hello3dprintingworld/helloprinter/Bed/Bed Corner Extruder x2.stl

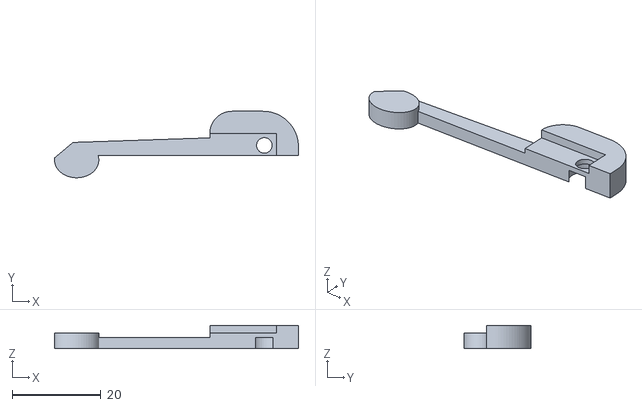
[picture p15: CAD file, 2015-12-08]
Bed/Bed Corner Extruder x2.stl
55.0 x 15.0 x 5.20
