hello3dprintingworld/helloprinter/Controllers/RAMPS 14/RAMPS FRONT.stl

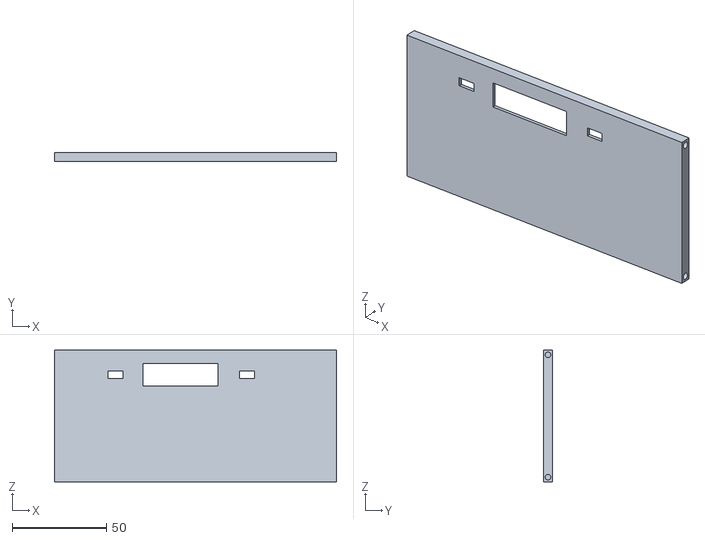
[picture p16: CAD file, 2014-11-10]
Controllers/RAMPS 14/RAMPS FRONT.stl
150.0 x 5.00 x 70.0
