hello3dprintingworld/helloprinter/Eixo X/5mm/x axis idler.stl

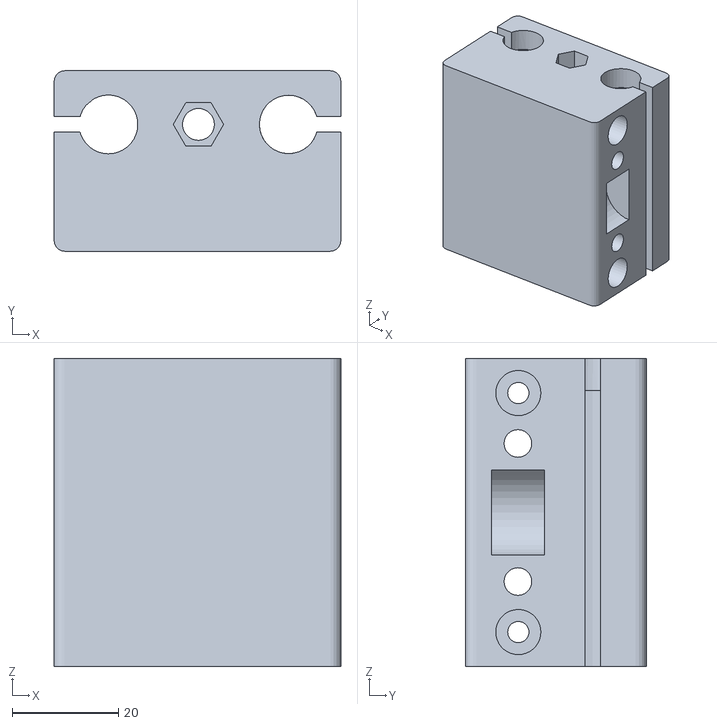
[picture p18: CAD file, 2015-12-08]
Eixo X/5mm/x axis idler.stl
54.0 x 34.0 x 58.0
