hello3dprintingworld/helloprinter/Eixo Z/Z motor x2.stl

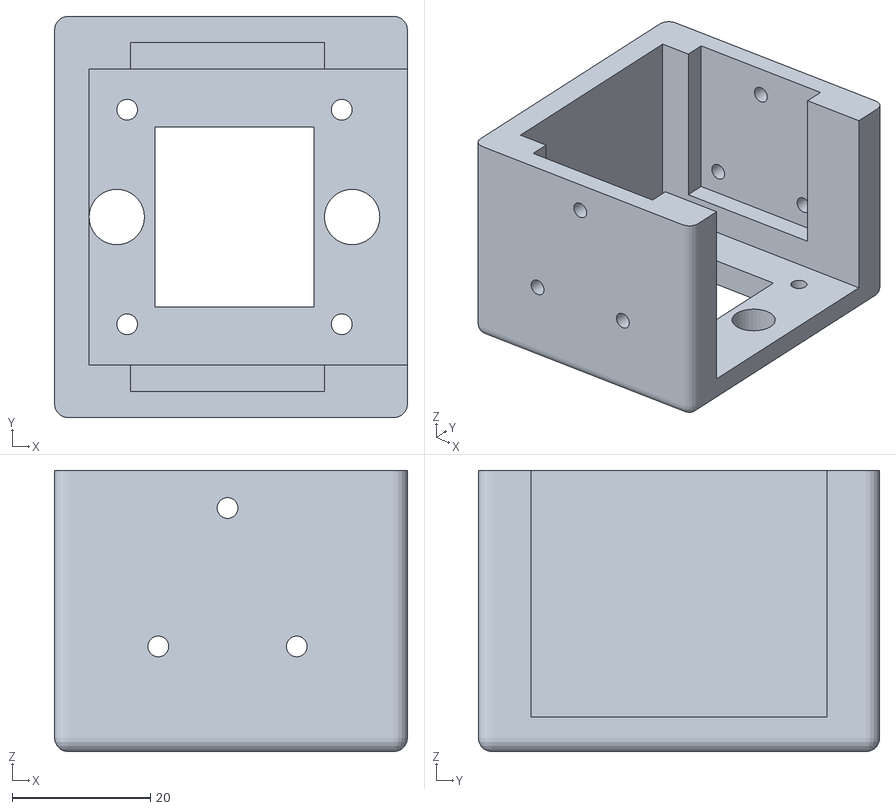
[picture p19: CAD file, 2015-12-08]
Eixo Z/Z motor x2.stl
51.0 x 58.0 x 40.6
