hello3dprintingworld/helloprinter/Endstops/endstop-holder-bottom x3.stl

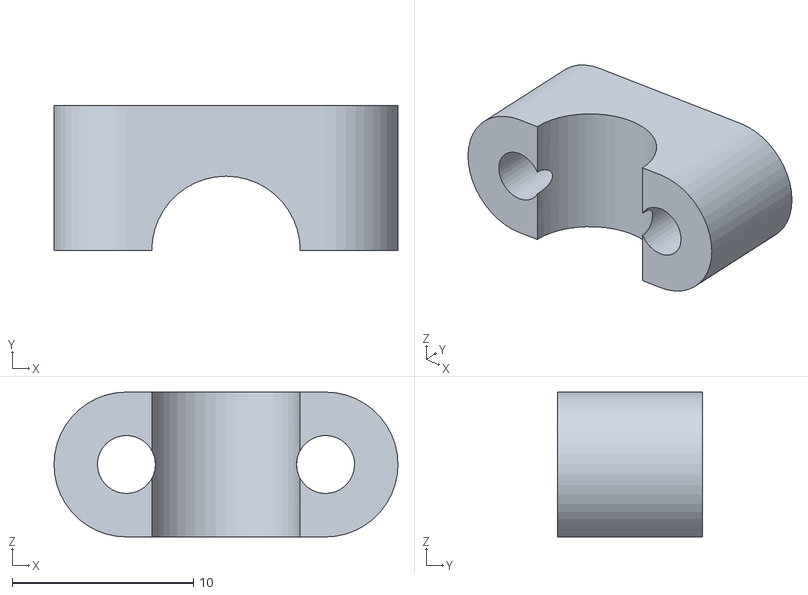
[picture p20: CAD file, 2015-12-08]
Endstops/endstop-holder-bottom x3.stl
19.0 x 8.00 x 8.00
