hello3dprintingworld/helloprinter/Extruder/Single Extruder for dual mirror parts/x belt.STL

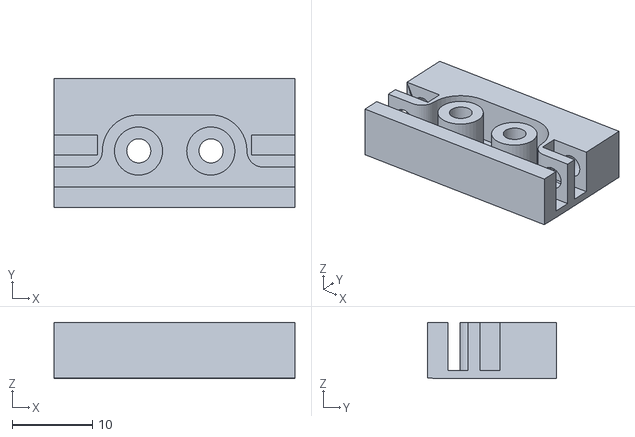
[picture p21: CAD file, 2015-12-08]
Extruder/Single Extruder for dual mirror parts/x belt.STL
30.0 x 16.0 x 7.00
