hello3dprintingworld/helloprinter/LCD/LCD Knob.stl

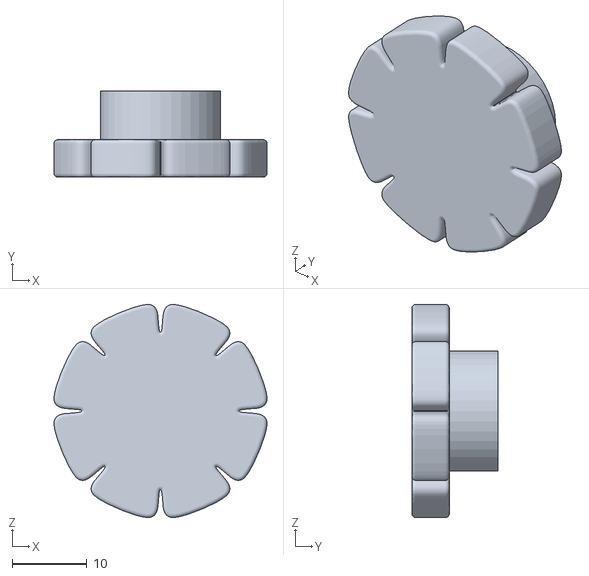
[picture p22: CAD file, 2014-11-10]
LCD/LCD Knob.stl
28.4 x 11.5 x 28.4
