hello3dprintingworld/helloprinter/Plug and switch/Plug and switch back x1.STL

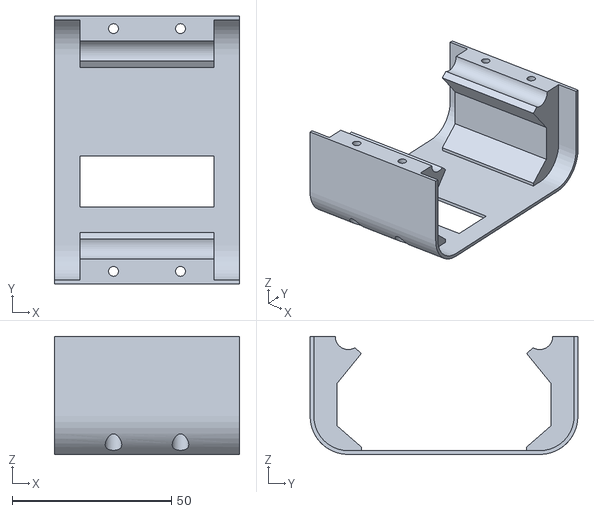
[picture p23: CAD file, 2015-12-08]
Plug and switch/Plug and switch back x1.STL
58.0 x 84.0 x 37.0
