hello3dprintingworld/helloprinter/Power Supply/PSU Cover x1.stl

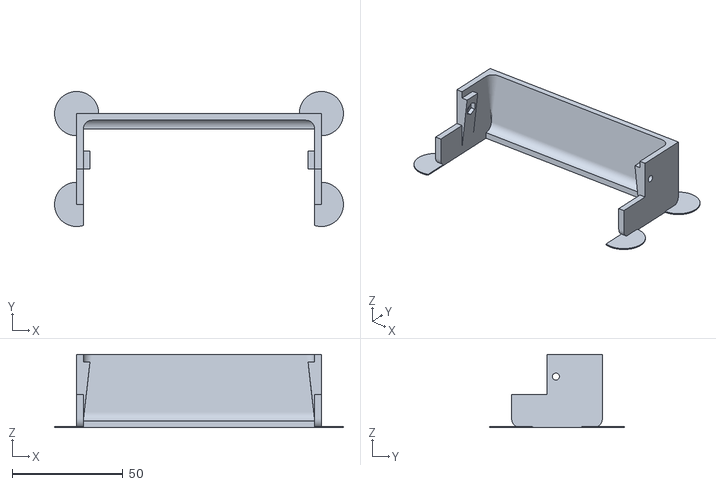
[picture p24: CAD file, 2015-12-08]
Power Supply/PSU Cover x1.stl
130.5 x 61.0 x 33.0
