hello3dprintingworld/helloprinter/Reinforcement XL/Part1.SLDPRT

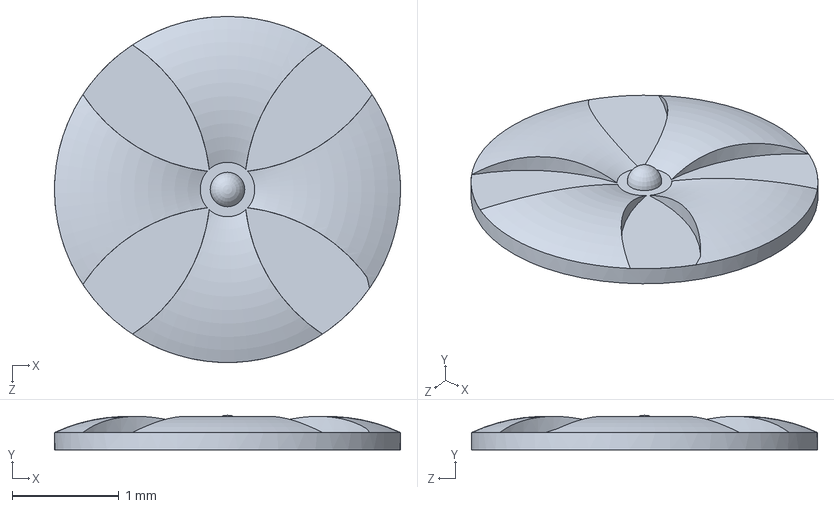
[picture p25: CAD file, 2015-12-08]
Reinforcement XL/Part1.SLDPRT
3.24 x 0.324 x 3.24 mm
