hello3dprintingworld/helloprinter/Spool Holder/Spool Holder.stl

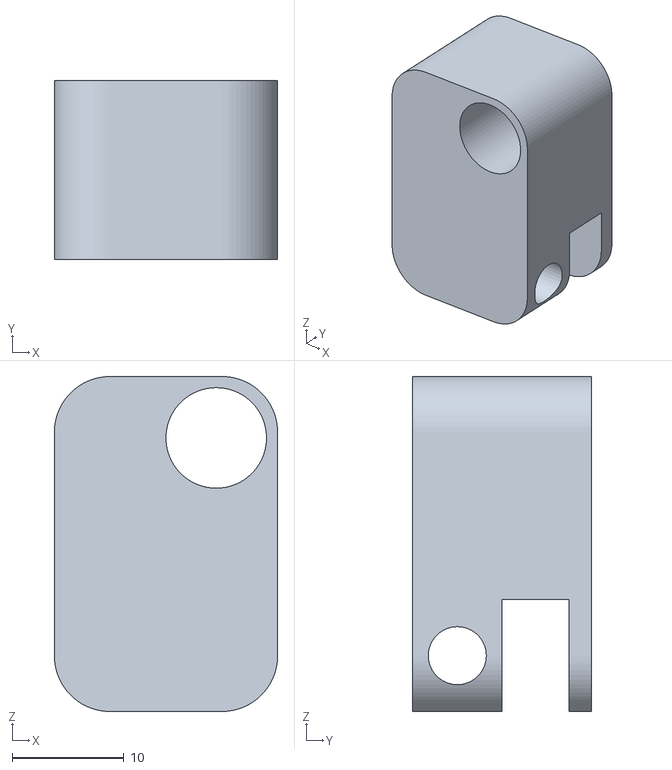
[picture p26: CAD file, 2015-12-08]
Spool Holder/Spool Holder.stl
20.0 x 16.0 x 30.0
