hello3dprintingworld/helloprinter/Bed/Bed corners normal x2.stl

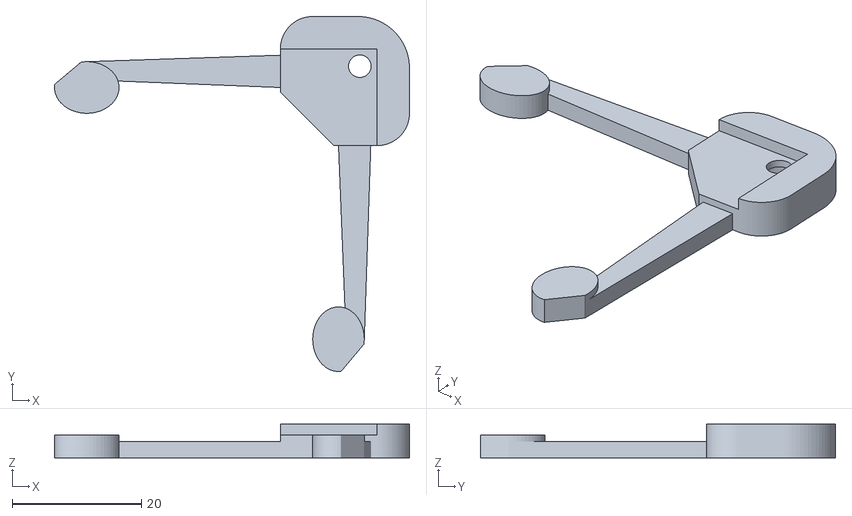
[picture p27: CAD file, 2015-12-08]
Bed/Bed corners normal x2.stl
55.0 x 55.0 x 5.20
