hello3dprintingworld/helloprinter/Controllers/RAMPS 14/RAMPS BOTTOM 1X.stl

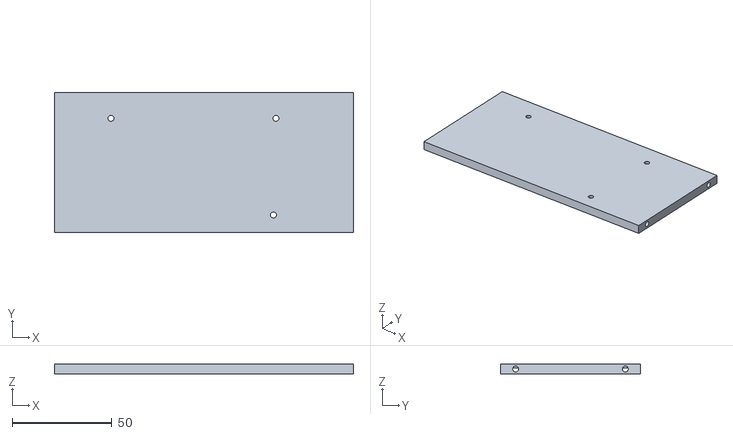
[picture p28: CAD file, 2014-11-10]
Controllers/RAMPS 14/RAMPS BOTTOM 1X.stl
150.0 x 70.0 x 5.00
