hello3dprintingworld/helloprinter/Controllers/RUMBA/LCD back.stl

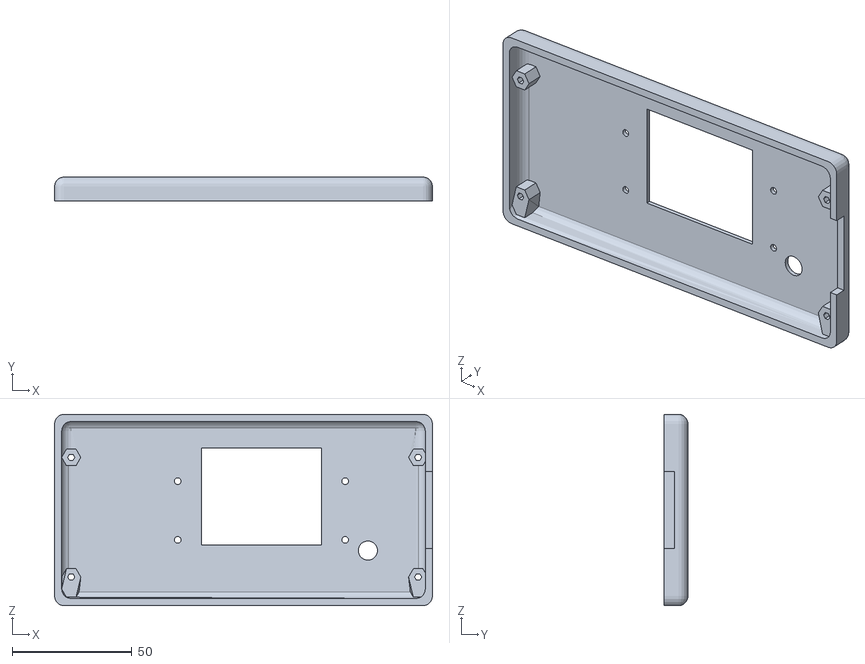
[picture p29: CAD file, 2015-12-08]
Controllers/RUMBA/LCD back.stl
158.0 x 10.1 x 80.0
