hello3dprintingworld/helloprinter/Eixo X/5mm/x axis idler tensioner.stl

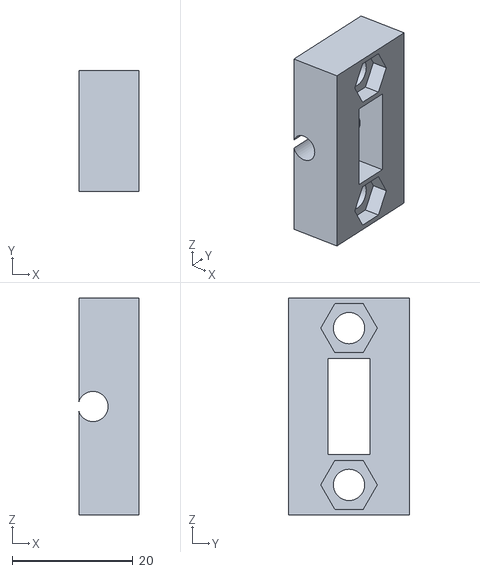
[picture p30: CAD file, 2015-12-08]
Eixo X/5mm/x axis idler tensioner.stl
10.0 x 20.0 x 36.0
