hello3dprintingworld/helloprinter/Eixo Y/Y Motor.stl

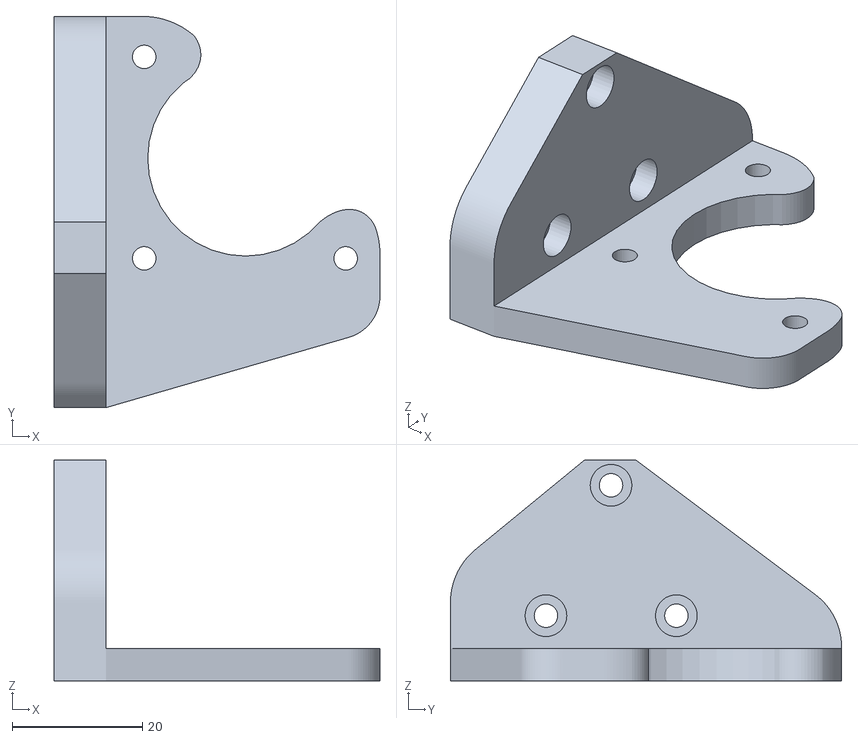
[picture p31: CAD file, 2014-07-07]
Eixo Y/Y Motor.stl
50.0 x 60.0 x 33.9
