hello3dprintingworld/helloprinter/Endstops/endstop-holder-top x3.stl

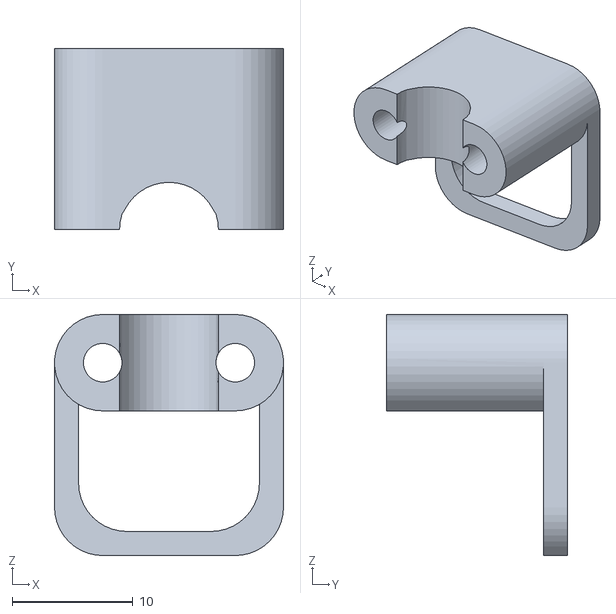
[picture p32: CAD file, 2015-12-08]
Endstops/endstop-holder-top x3.stl
19.0 x 15.0 x 20.0
