hello3dprintingworld/helloprinter/Extruder/Single Extruder for dual mirror parts/fan.STL

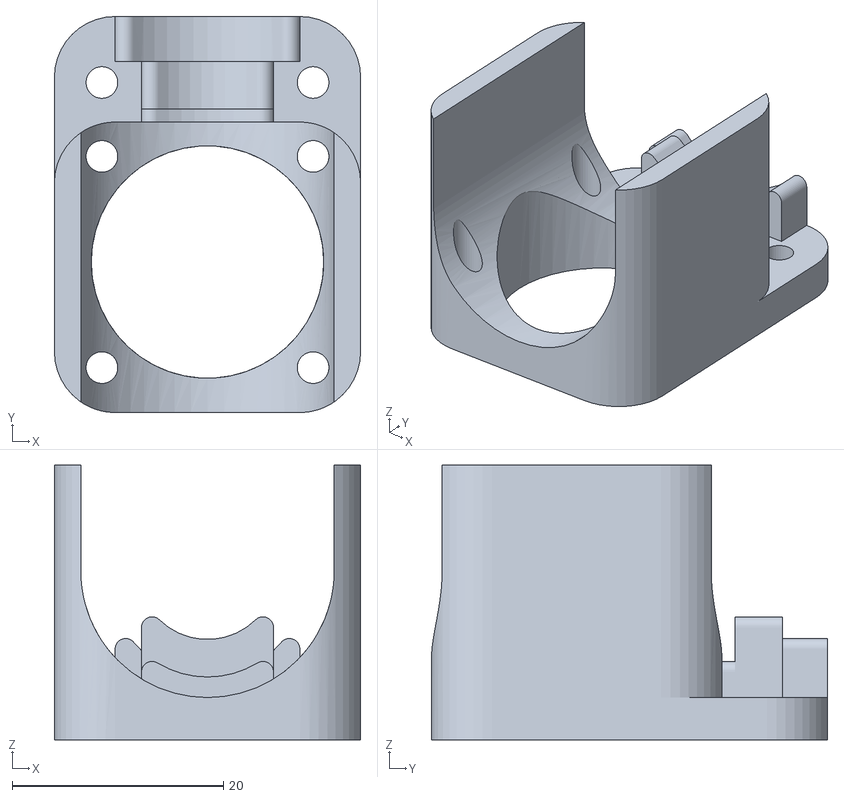
[picture p33: CAD file, 2015-12-08]
Extruder/Single Extruder for dual mirror parts/fan.STL
29.0 x 37.5 x 26.0
