hello3dprintingworld/helloprinter/Power Supply/Cable Guide BED.stl

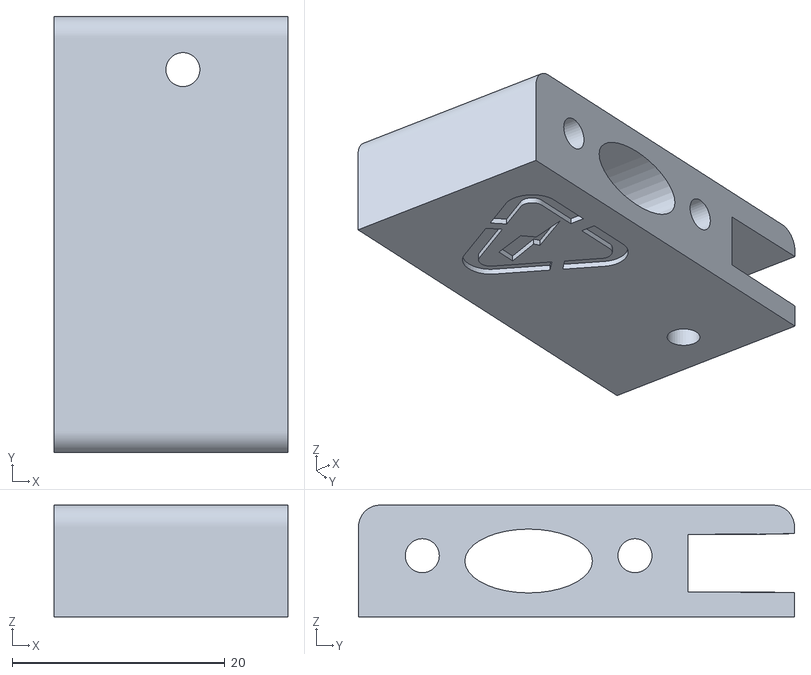
[picture p34: CAD file, 2015-12-08]
Power Supply/Cable Guide BED.stl
22.0 x 41.0 x 10.5
