hello3dprintingworld/helloprinter/Reinforcement XL/locker.STL

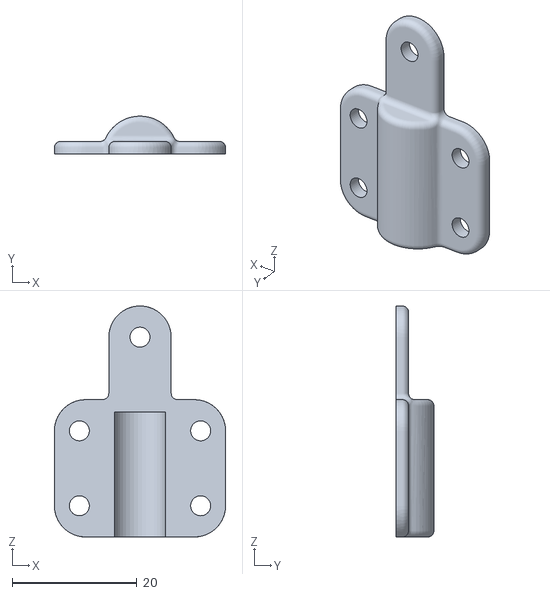
[picture p35: CAD file, 2015-12-08]
Reinforcement XL/locker.STL
27.4 x 6.05 x 37.0
