hello3dprintingworld/helloprinter/Spool Holder/LinearBearing.stl

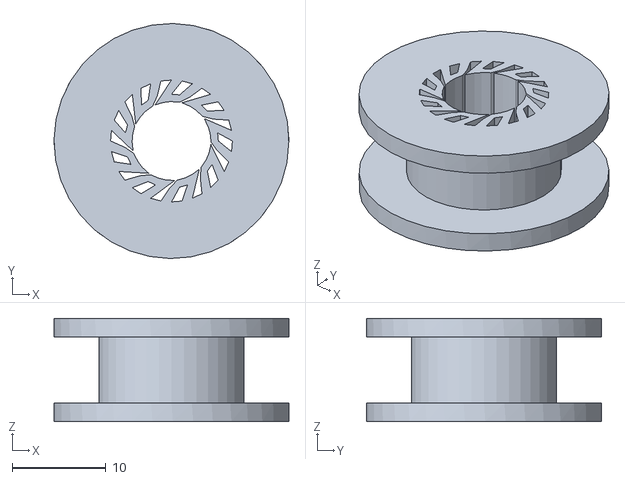
[picture p36: CAD file, 2015-12-08]
Spool Holder/LinearBearing.stl
25.1 x 25.1 x 11.0
