hello3dprintingworld/helloprinter/Bed/i3_Adj_Y_Low_P_holder_02.stl

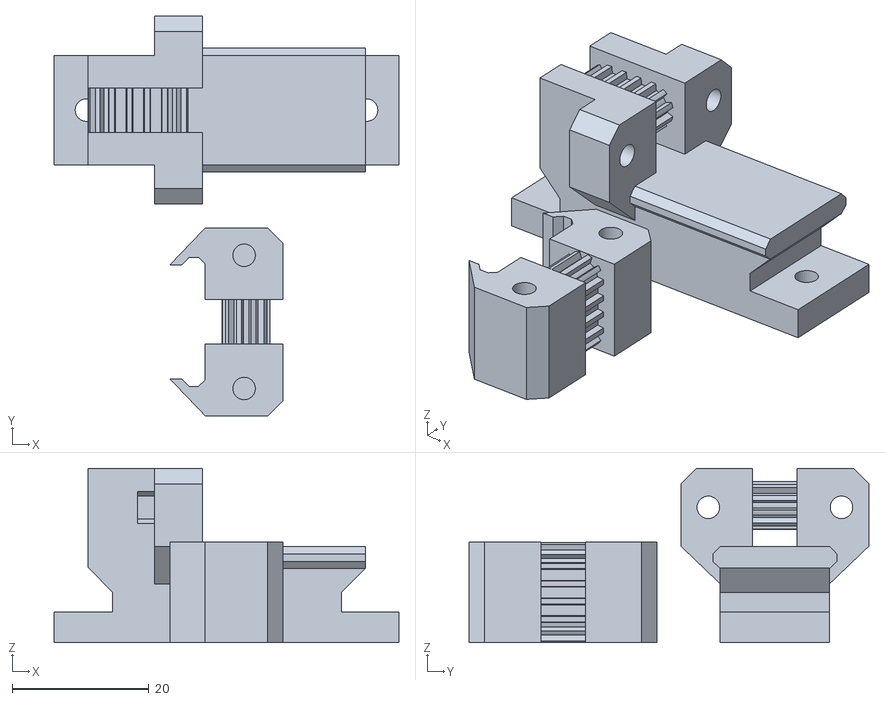
[picture p37: CAD file, 2014-07-07]
Bed/i3_Adj_Y_Low_P_holder_02.stl
50.5 x 58.5 x 25.5
