hello3dprintingworld/helloprinter/Controllers/RUMBA/Power Box Rumba LAT1.stl

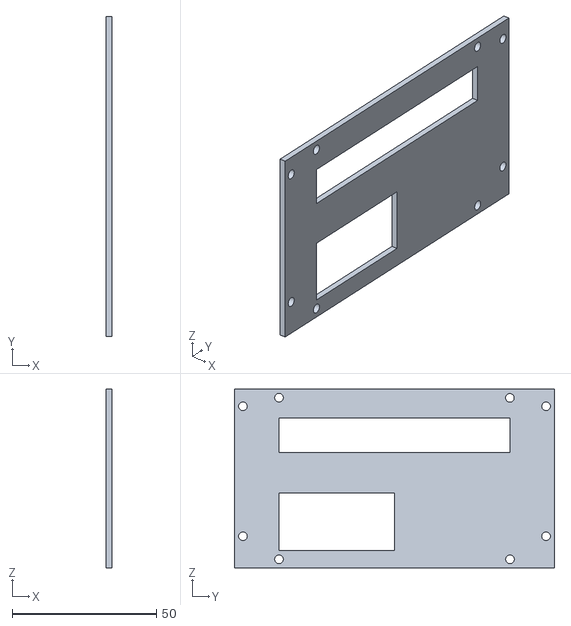
[picture p39: CAD file, 2015-12-08]
Controllers/RUMBA/Power Box Rumba LAT1.stl
2.00 x 111.0 x 62.0
