hello3dprintingworld/helloprinter/Extruder/Single Extruder for dual mirror parts/extruder - 1-50F.STL

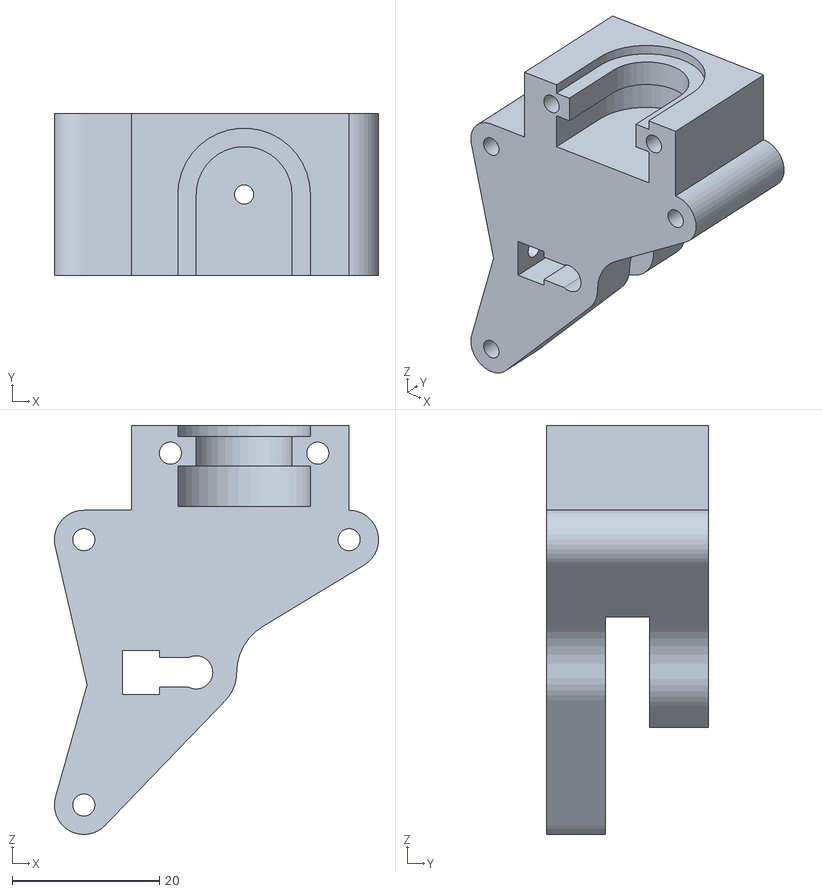
[picture p40: CAD file, 2015-12-08]
Extruder/Single Extruder for dual mirror parts/extruder - 1-50F.STL
44.0 x 22.0 x 55.5
