hello3dprintingworld/helloprinter/Power Supply/Frame cable connection back.stl

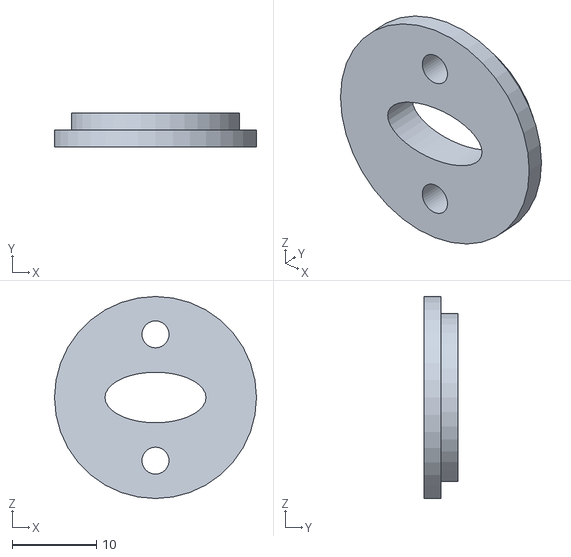
[picture p41: CAD file, 2015-12-08]
Power Supply/Frame cable connection back.stl
24.0 x 4.00 x 24.0
