hello3dprintingworld/helloprinter/Controllers/RAMPS 14/RAMPS LAT2.stl

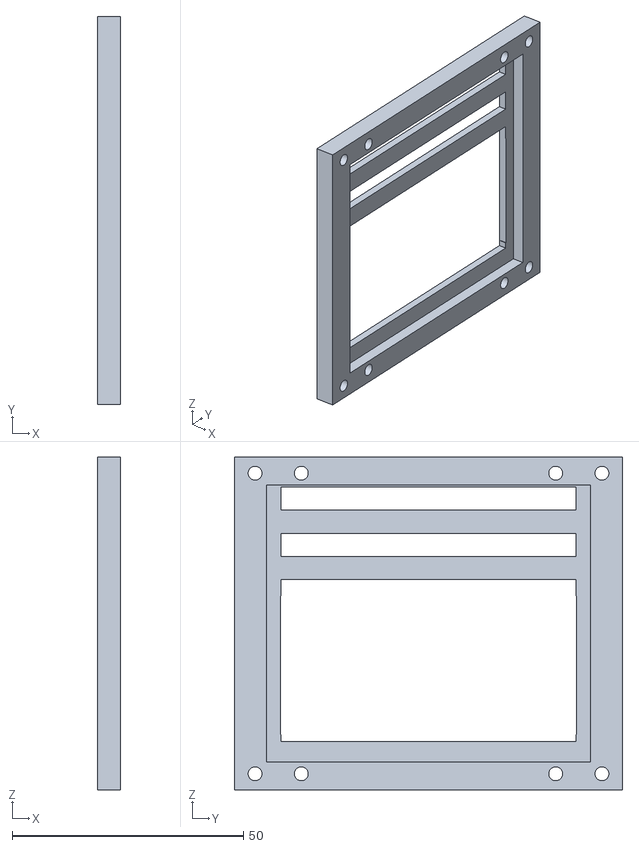
[picture p42: CAD file, 2014-11-10]
Controllers/RAMPS 14/RAMPS LAT2.stl
5.00 x 84.0 x 72.0
