hello3dprintingworld/helloprinter/Controllers/RUMBA/Power Box Rumba TOP.stl

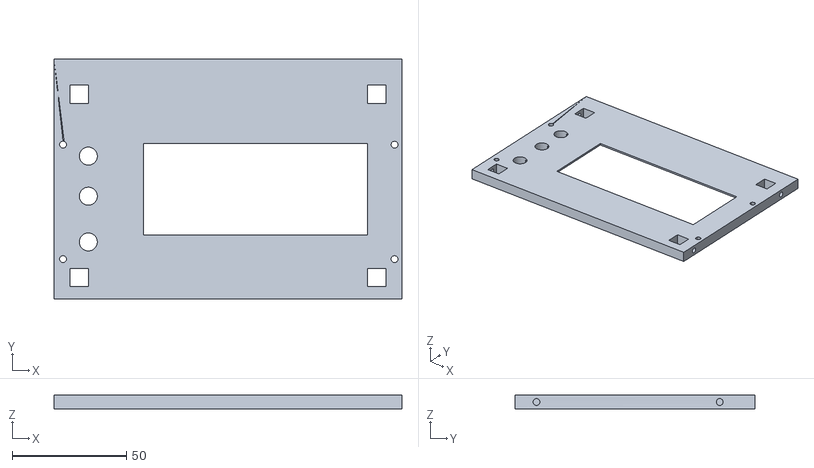
[picture p43: CAD file, 2015-12-08]
Controllers/RUMBA/Power Box Rumba TOP.stl
152.0 x 105.0 x 6.00
