hello3dprintingworld/helloprinter/Power Supply/PSU Support v2 x4.stl

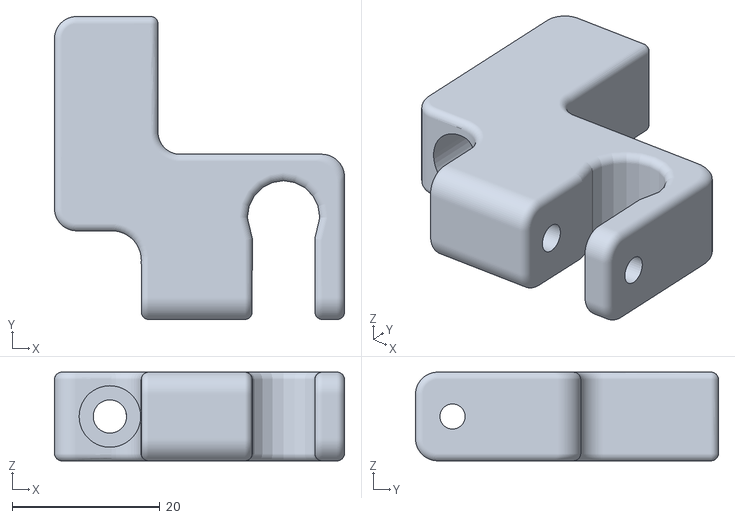
[picture p44: CAD file, 2015-12-08]
Power Supply/PSU Support v2 x4.stl
39.2 x 41.0 x 12.0
