hello3dprintingworld/helloprinter/Controllers/RAMPS 14/RAMPS TOP.stl

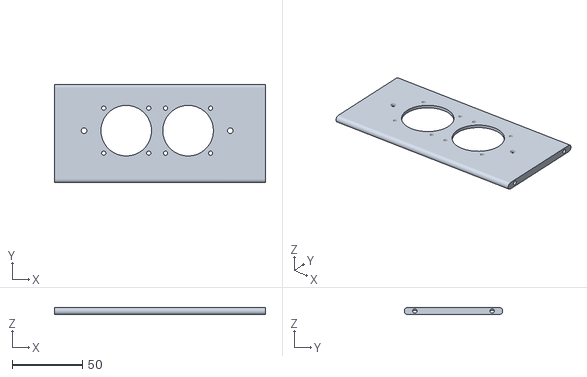
[picture p45: CAD file, 2014-11-10]
Controllers/RAMPS 14/RAMPS TOP.stl
150.0 x 70.0 x 5.00
