hello3dprintingworld/helloprinter/Controllers/RUMBA/Power Box Rumba FRONT 2.stl

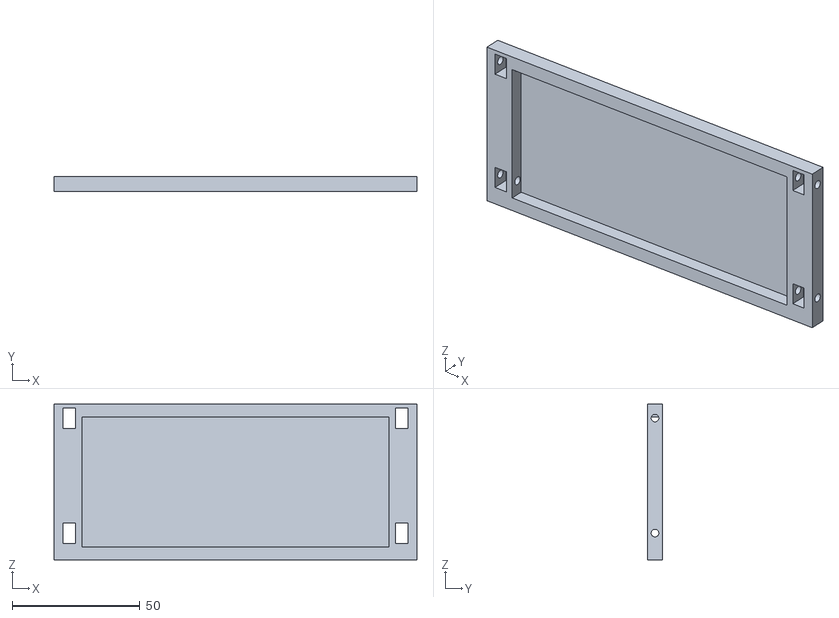
[picture p46: CAD file, 2015-12-08]
Controllers/RUMBA/Power Box Rumba FRONT 2.stl
142.0 x 6.00 x 61.0
