hello3dprintingworld/helloprinter/Power Supply/Cable Guide.stl

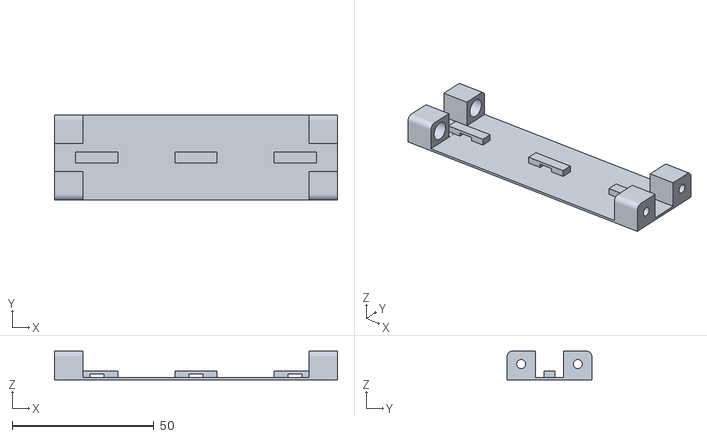
[picture p47: CAD file, 2015-12-08]
Power Supply/Cable Guide.stl
100.0 x 30.0 x 10.2
