hello3dprintingworld/helloprinter/Controllers/RUMBA/Power Box Rumba LAT2.stl

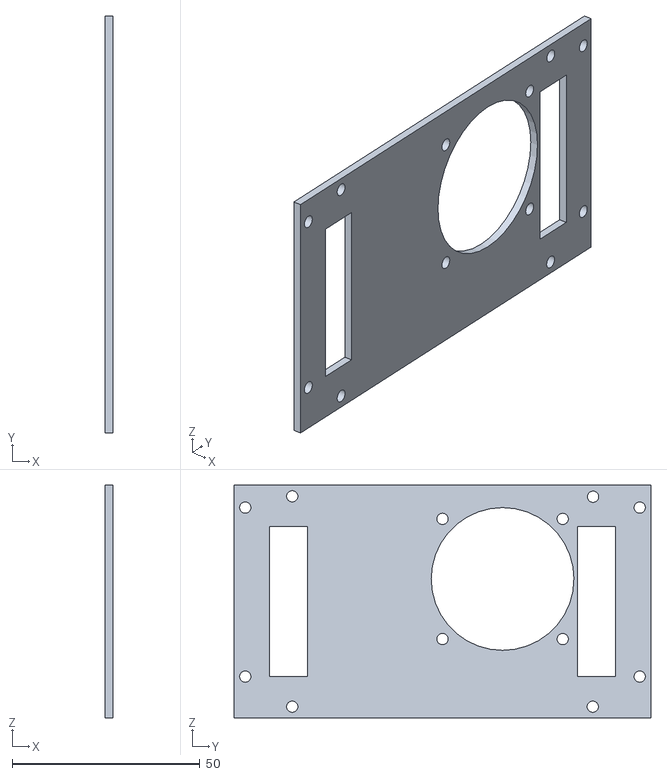
[picture p48: CAD file, 2015-12-08]
Controllers/RUMBA/Power Box Rumba LAT2.stl
2.00 x 111.0 x 62.0
