hello3dprintingworld/helloprinter/Power Supply/PSU Support x4.stl

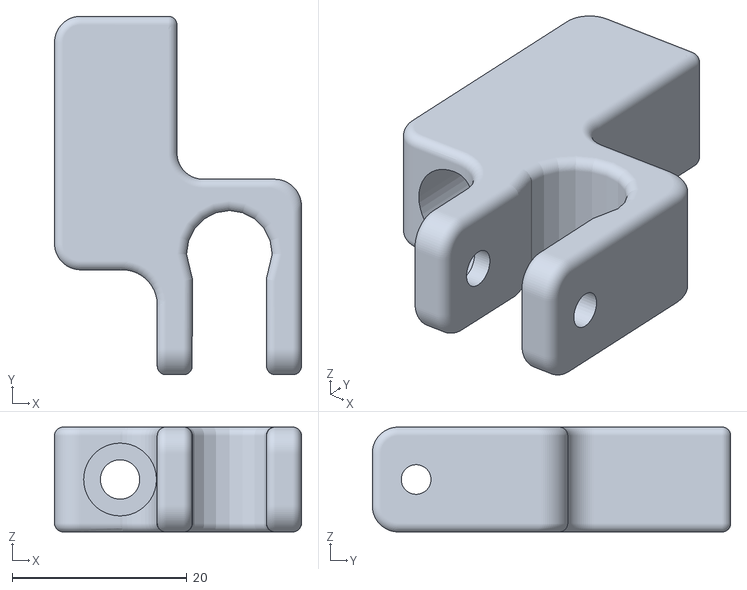
[picture p49: CAD file, 2015-12-08]
Power Supply/PSU Support x4.stl
28.3 x 41.0 x 12.0
