hello3dprintingworld/helloprinter/Controllers/RUMBA/Power Box Rumba Support.stl

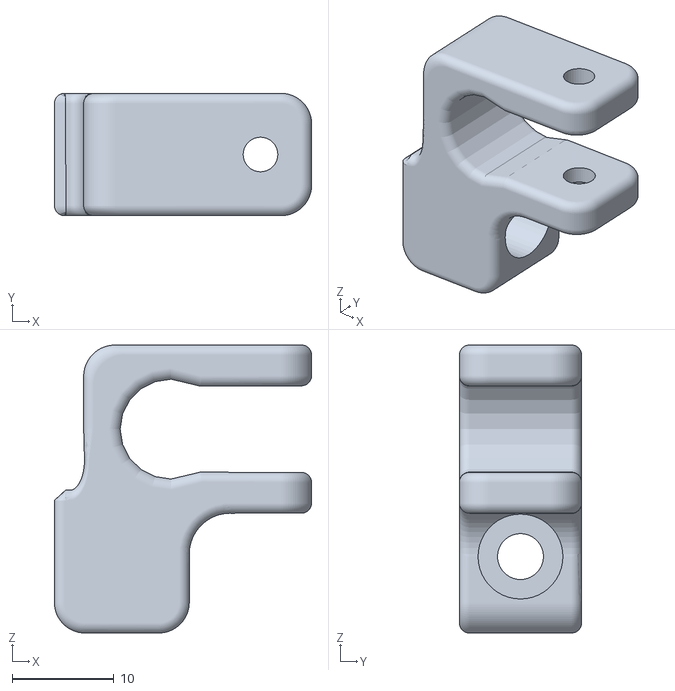
[picture p50: CAD file, 2015-12-08]
Controllers/RUMBA/Power Box Rumba Support.stl
25.2 x 12.0 x 28.3
